sdp8483/Keithley_17X_USB/enclosure/FreeCAD/Keithley_17X_USB_Bottom.FCStd

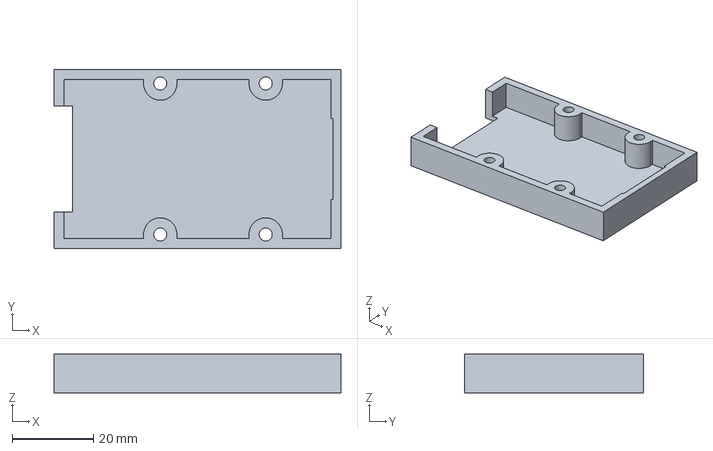
[picture p43: CAD file, 2019-03-24]
enclosure/FreeCAD/Keithley_17X_USB_Bottom.FCStd
70.5 x 44.0 x 9.53 mm
