sdp8483/Keithley_17X_USB/pcb/3d_models/0ZCJ.step

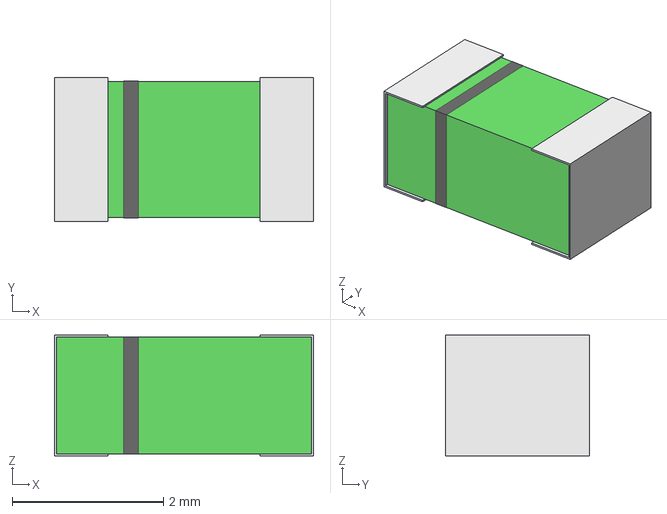
[picture p44: CAD file, 2019-02-24]
pcb/3d_models/0ZCJ.step
3.43 x 1.90 x 1.60 mm
