sdp8483/Keithley_17X_USB/pcb/3d_models/SOIC-16_3.9x9.9mm_P1.27mm.step

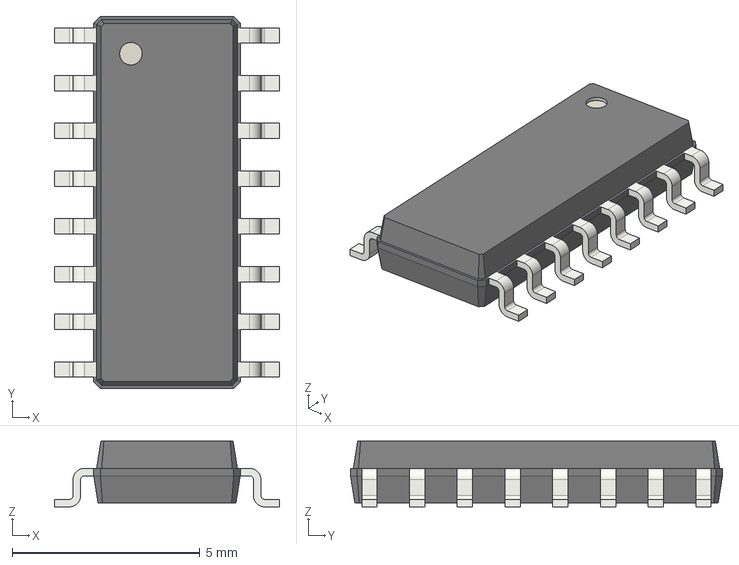
[picture p45: CAD file, 2019-02-24]
pcb/3d_models/SOIC-16_3.9x9.9mm_P1.27mm.step
6.00 x 9.90 x 1.75 mm
