sdp8483/Keithley_17X_USB/pcb/3d_models/USB_B_RightAngle.step

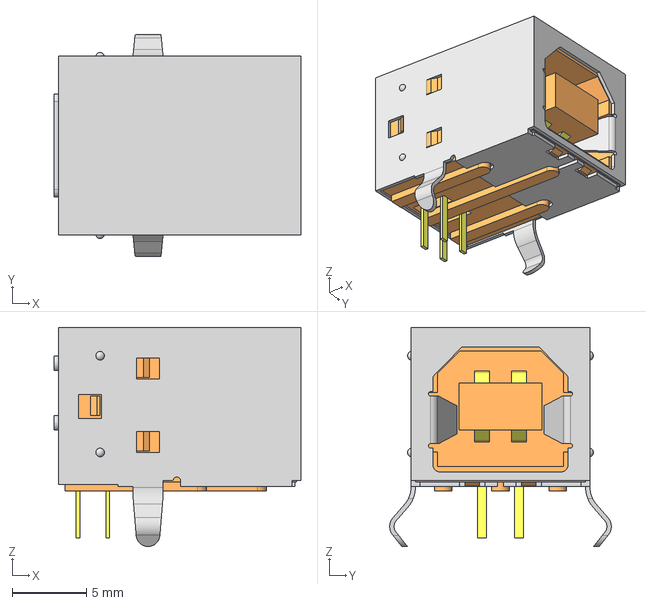
[picture p46: CAD file, 2019-02-23]
pcb/3d_models/USB_B_RightAngle.step
16.6 x 14.9 x 14.7 mm
