sdp8483/Keithley_17X_USB/pcb/3d_models/Keystone_7761.step

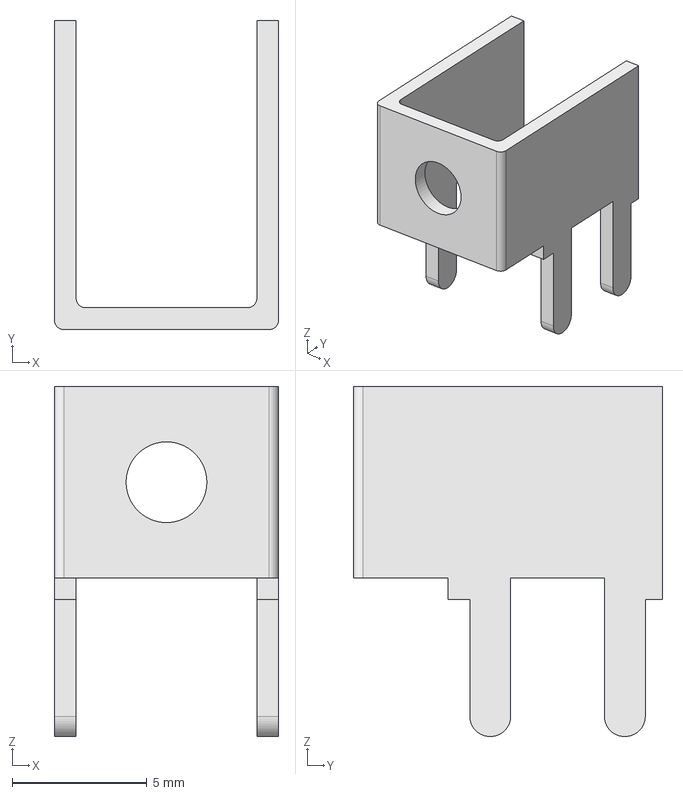
[picture p47: CAD file, 2019-02-19]
pcb/3d_models/Keystone_7761.step
8.33 x 11.5 x 13.0 mm
