sdp8483/Keithley_17X_USB/firmware/keithley_17X_USB/keithley.h

/*
 * keithley.h
 *
 *  Created on: Feb 10, 2019
 *      Author: Sam
 */

#ifndef KEITHLEY_H_
#define KEITHLEY_H_

#define OVER_RANGE_ACTIVE   0
#define OVER_RANGE_INACTIVE BIT1

void read_databus(char *string);

#endif /* KEITHLEY_H_ */
